vmj1108/open-source-rover/examples/images/AUDACITY/Houston-Robotics-Fidelity cropped.jpg

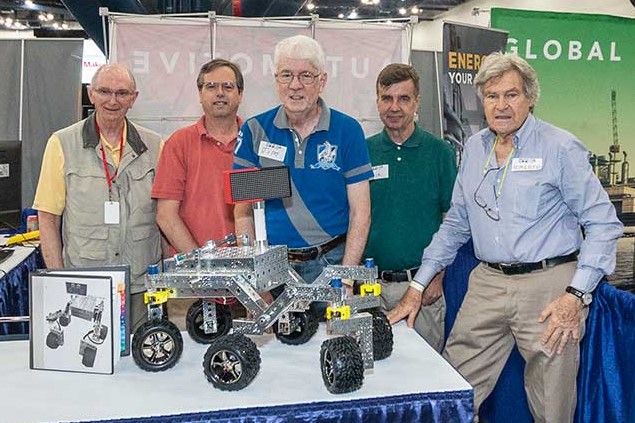
examples/images/AUDACITY/Houston-Robotics-Fidelity cropped.jpg
