vmj1108/open-source-rover/examples/images/AUDACITY/IMG_3931.JPG

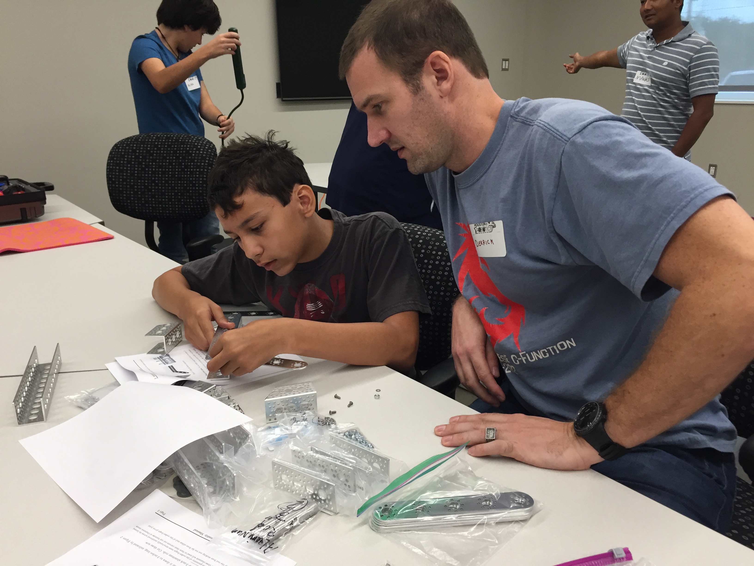
examples/images/AUDACITY/IMG_3931.JPG
