vmj1108/open-source-rover/examples/images/AUDACITY/IMG_4751.JPG

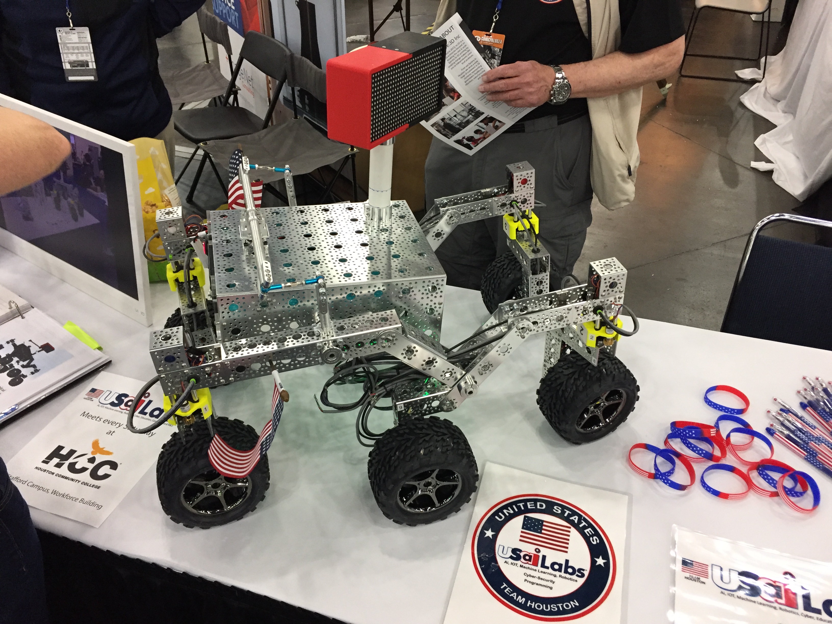
examples/images/AUDACITY/IMG_4751.JPG
